HackLab-Oriente/desktop-buddy/docs/services.md

# Servicios de terceros: qué necesitamos y recomendaciones

Precios verificados el 2026-07-13. El contrato de Brain mantiene todo esto
intercambiable — son valores por defecto, no compromisos. Todas las claves
viven en la NVS del dispositivo, se meten por la web UI y nunca van en packs.

## Servicios que necesita el buddy

| Servicio | Para qué | Cuándo | ¿Cuenta? |
|---|---|---|---|
| **LLM** (el Brain) | Personalidad, conversación, elección de emoción | v1 (M2) | Sí |
| **STT** (voz a texto) | Entrada de voz push-to-talk | v1 (M3) | Sí |
| **TTS** (texto a voz) | Respuestas habladas | v1 (M3) | Sí |
| Hora NTP | Reloj, timers, comportamientos de reposo | v1 | No (pool.ntp.org, gratis) |
| Calendario/feeds por polling | Senses opcionales (ICS, RSS) | v2 | No (URLs públicas o con token) |
| Relay de webhooks / túnel | Eventos entrantes sin IP pública | v2 (era del hub) | Capas gratuitas (Cloudflare Tunnel, Tailscale) |

## LLM — el Brain

| Proveedor / modelo | Precio (in/out por MTok) | Por qué sí / por qué no |
|---|---|---|
| **Anthropic Claude Haiku 4.5** ⭐ | $1 / $5 | Rápido, barato y con carácter — para un compañero, la calidad de la personalidad ES el producto. Streaming. **El prompt caching no aplica todavía** — ver abajo. |
| OpenAI clase gpt-4o-mini | ~$0.60 / $2.40 | Algo más barato; su atractivo real es la comodidad de una sola cuenta (ver stacks abajo). |
| Anthropic Claude Sonnet 5 | $3 / $15 ($2/$10 intro) | Sobredimensionado para charla ligera; interesante después para Skills/herramientas en el hub. |

Una interacción típica, **medida sobre el cuerpo que envía el firmware hoy**:
~200 tokens de entrada y ~45 de salida → **~$0.0004 con Haiku**. La estimación
anterior (1.200 in / 150 out, ~$0.002) era unas 4,6 veces pesimista.

**El prompt caching no recorta nada con este prompt.** El prefijo mínimo
cacheable de Claude Haiku 4.5 son **4.096 tokens** y el system prompt de
personalidad son ~160: veinticinco veces corto, así que un `cache_control`
se ignoraría en silencio. Y aunque aplicara, a 50 interacciones diarias
ahorraría ~$0,22 al mes — y como el TTL por defecto son 5 minutos, un buddy
al que se acaricia cada pocas horas fallaría la caché casi siempre y pagaría
el recargo de escritura de 1,25×, saliendo **más caro**.

Mantener el prompt estable byte a byte sigue siendo buena práctica; el ahorro
llega el día que un pack empuje el system prompt más allá de 4.096 tokens
(~16 KB de texto), no antes.

## STT — de voz a texto

La clave: **push-to-talk elimina la necesidad de STT en streaming en v1.**
Soltar el botón = fin de la frase, así que el dispositivo puede hacer un POST
HTTPS con el clip completo (unos segundos de WAV) y recibir el texto. Eso es
radicalmente más simple en el ESP32 que un WebSocket de streaming — un POST
multipart con `esp_http_client` y ya.

| Proveedor | Precio | Modo | Encaje en ESP32 |
|---|---|---|---|
| **OpenAI gpt-4o-mini-transcribe** ⭐ | ~$0.003/min ($0.18/hora) | POST por lotes (existe variante realtime) | **Mismo host que el TTS**: una clave, un certificado, una conexión TLS reutilizable. Ver abajo. |
| Groq Whisper large-v3-turbo | $0.04/hora, **facturación mínima de 10 s por petición** | POST por lotes, ~217× tiempo real (un clip de 5 s se transcribe en decenas de ms) | Inferencia mucho más rápida y capa gratuita real (2.000 peticiones/día). Un host TLS más, y 20 req/min **por organización**. |
| Deepgram Nova-3 | $0.0048/min streaming | Streaming por WebSocket | Ver fila de abajo. |

### Por qué el STT cambió de Groq a OpenAI

La primera versión de este documento elegía Groq por precio. El análisis no
estaba mal; el precio resultó ser el eje **menos** importante a nuestra escala.

**El precio no decide.** El titular de Groq es $0,04/h contra $0,18/h — 4,5×
más barato. Pero Groq **factura un mínimo de 10 s por petición**, y un buddy
push-to-talk manda clips de 2–5 s. Por debajo de **2,2 s OpenAI sale más
barato**, y en la duración típica la diferencia se queda en 1,4×. Un taller
entero —15 personas, 4 sesiones, ~30 interacciones cada una— son **1.800
transcripciones: $0,20 con Groq contra $0,27 con OpenAI. Siete centavos.**

**Lo que sí decide: un host TLS menos.** Cada turno de voz habla con STT →
Claude → TTS. Con Groq son **tres hosts distintos**; con OpenAI haciendo STT y
TTS son **dos**, y esa conexión se puede mantener viva a través de la llamada
al cerebro. Importa porque una conexión TLS cuesta **~50 KB de RAM interna**
(ver [architecture.md](architecture.md)), justo la memoria escasa —los búferes
DMA y el WiFi no pueden vivir en PSRAM—, y porque un handshake mbedTLS en el
ESP32 se mide en cientos de milisegundos contra un presupuesto total de
1,5–3 s. Groq gana en inferencia (decenas de ms contra unos cientos), pero ese
ahorro es más pequeño que un handshake entero.

> **Esto último está sin medir.** Es la única cifra que podría darle la vuelta
> a la decisión: si el handshake resulta barato con reanudación de sesión,
> Groq gana por velocidad. Medirlo es tarea del track de voz.

**La trampa de la capa gratuita.** Groq regala 2.000 peticiones/día sin
tarjeta, que para un hacklab vale. Pero el límite son **20 peticiones/minuto
por organización**, y varias claves no lo multiplican: 15 personas pulsando
cada 30 s son 30 req/min, **por encima del límite**. Solo funciona si cada uno
se hace su propia cuenta, que es un paso más de instalación por quince.

**Qué haría cambiar la decisión:** transcripción larga (grabar una reunión, no
una frase), donde el 4,5× de Groq sí es dinero; o un handshake medido barato.

## ¿Y hacer todo el flujo con un solo proveedor?

**Con Anthropic no se puede: no tiene STT ni TTS.** Su API es texto e imagen de
entrada, texto de salida. Claude puede ser el cerebro; nunca los oídos ni la
boca.

**Y el cerebro no se mueve a OpenAI solo por fontanería.** El argumento del host
TLS que ganó para el STT pierde aquí: transcribir y hablar son commodities
—cambiar de proveedor cambia una cifra en la factura— mientras que **el cerebro
es la única pieza cuya elección se *oye* como personalidad**, que es lo que este
proyecto dice estar vendiendo. La diferencia de coste son ~$1,80 en todo el
taller, y mantener la opción abierta ya está pagado: el contrato de cerebro es
un adaptador con backends intercambiables.

## TTS — de texto a voz

Restricción: el ESP32 quiere **PCM o MP3 en streaming de vuelta** (decodificar
MP3 con libhelix/minimp3 es barato; PCM crudo a 16k/22k es aún más fácil).
Los tres de abajo pueden dar ambos.

| Proveedor | Precio | Por qué sí / por qué no |
|---|---|---|
| **OpenAI gpt-4o-mini-tts** ⭐ | ~$0.015/min de audio ($0.60/MTok texto de entrada, $12/MTok audio de salida) | Barato, buena calidad, ~13 voces, admite "instrucciones" de voz (tono/carácter — útil para packs de personalidad). |
| Groq PlayAI Dialog / Orpheus | $50 / $22 por millón de caracteres | Orpheus sale barato, pero devuelve el tercer host TLS y sus variantes publicadas son inglés y árabe — **para un buddy que habla español hay que verificarlo antes de considerarlo**. |
| ElevenLabs Flash v2.5 | $0.05/1k caracteres, **con mínimo de facturación de 1.000 caracteres** | Las mejores voces con carácter + clonado, y 75 ms de latencia. Pero una respuesta de 150 caracteres factura como 1.000: **$0,05 por respuesta, 20× OpenAI** (ver abajo). |
| Deepgram Aura-2 | ~$0.03–0.05/1k caracteres | Baja latencia, API simple; atractivo de bundle si ya estás en Deepgram para STT. |

### El TTS es donde está el dinero — y el mínimo de ElevenLabs

Una respuesta hablada del buddy son ~150 caracteres (~10 s de audio). Con eso:

| TTS | por respuesta | taller (1.800) | ×OpenAI |
|---|---|---|---|
| **OpenAI gpt-4o-mini-tts** ⭐ | $0,0025 | **$4,50** | 1× |
| Groq Orpheus (inglés) | $0,0033 | $5,94 | 1× |
| Groq PlayAI Dialog | $0,0075 | $13,50 | 3× |
| ElevenLabs Flash v2.5 | $0,0500 | **$90,00** | **20×** |

Dos cosas que corregir de la versión anterior de este documento:

1. **ElevenLabs decía «≈$0,0075 por respuesta»: era 6,7× optimista.** Dividía la
   tarifa y no veía el **mínimo de 1.000 caracteres por petición**. Nuestras
   respuestas son de 150.
2. **El TTS cuesta ~17× lo que el STT.** Toda la discusión de Groq contra
   OpenAI para transcribir se peleaba por siete centavos mientras el gasto real
   estaba en la fila de abajo.

> **Regla, no anécdota: mira siempre el mínimo de facturación antes que la
> tarifa.** Nos ha pasado dos veces —los 10 s de Groq en STT, los 1.000
> caracteres de ElevenLabs en TTS— y las dos veces el titular mentía. Un buddy
> habla a ráfagas de una frase; a esa escala **el mínimo manda sobre la
> tarifa**. Cualquier proveedor nuevo se evalúa con el coste de *una respuesta
> nuestra*, no con el precio por hora o por millón.

**ElevenLabs no está descartado: está aplazado.** $90 por taller es asequible
si el grupo decide que una voz propia *es* el producto — eso es una decisión de
personalidad, no un problema de presupuesto. La razón para esperar es otra:
**todavía nadie sabe cómo debe sonar el buddy.** Mientras tanto, el parámetro
`instructions` de OpenAI deja que cada pack ajuste el tono. Se revisa cuando
[#24](https://github.com/HackLab-Oriente/desktop-buddy/issues/24) y las
decisiones de personalidad hayan producido un carácter concreto.

## Coste por interacción (el número que importa)

Un intercambio PTT ≈ 8 s de voz del usuario + respuesta hablada de ~150
caracteres:

| Pieza | Stack recomendado | Coste |
|---|---|---|
| STT (OpenAI mini-transcribe) | 8 s a $0.003/min | ~$0.0004 |
| LLM (Haiku 4.5) | ~200 in / 45 out | ~$0.0004 |
| TTS (OpenAI mini-tts) | ~10 s de audio | ~$0.0025 |

El TTS es la partida más grande de las tres — y con ElevenLabs sería **$0,05**,
veinte veces el total actual.
| **Total** | | **≈ medio centavo** |

Con un uso intenso de 50 interacciones/día: **~$7/mes por buddy**. Las
interacciones solo-chirp (reflejos, gestos) no cuestan nada; el chat de texto
por web solo paga la parte del LLM.

## Stacks recomendados

- **Recomendado:** Claude Haiku 4.5 (cerebro) + OpenAI para **voz entera**
  (mini-transcribe + mini-tts). **Dos cuentas y dos hosts TLS**, no tres. La
  diferencia de coste contra meter Groq es de centavos; la de fontanería, no.
- **Menos cuentas (para amigos):** solo OpenAI — gpt-4o-mini (cerebro) +
  gpt-4o-mini-transcribe + gpt-4o-mini-tts. Una sola clave que pegar en la
  web UI. La web debería soportar ambos presets; el contrato de Brain hace
  que el proveedor sea un desplegable, no un fork.
- **Mejora de voz con carácter:** cambia el TTS a ElevenLabs Flash v2.5
  cuando un pack quiera una voz distintiva.

## Notas de implementación

- **El streaming de la respuesta del LLM importa más que el del STT.**
  Streamea la respuesta de Haiku para que la cara/emoción reaccione según
  llega el texto, y el TTS pueda empezar con la primera frase — ahí se gana
  la latencia percibida.
- **Prompt caching:** mantén el system prompt de personalidad estable byte a
  byte para que la caché de Anthropic recorte ~90% del coste de entrada en
  interacciones repetidas.
- Todos los proveedores de aquí son TLS + token bearer sobre HTTPS/WebSocket
  — todo amigable para el ESP32; no hace falta baile OAuth en v1 (las
  integraciones OAuth-osas son exactamente para lo que existe el hub de v2).

### Fuentes

- [Precios de Deepgram](https://deepgram.com/pricing) · [Desglose de tarifas Nova-3](https://brasstranscripts.com/blog/deepgram-pricing-per-minute-2025-real-time-vs-batch)
- [Groq Whisper large-v3-turbo](https://groq.com/blog/whisper-large-v3-turbo-now-available-on-groq-combining-speed-quality-for-speech-recognition) · [Guía de precios de Groq](https://www.eesel.ai/blog/groq-pricing)
- [Precios de transcripción de OpenAI](https://costgoat.com/pricing/openai-transcription) · [Precios de gpt-4o-mini-tts](https://tokenmix.ai/blog/gpt-4o-mini-tts-cheapest-tts-api-2026)
- [Precios de la API de ElevenLabs](https://elevenlabs.io/pricing/api)
- Precios de modelos Anthropic: docs de la Claude API (Haiku 4.5 $1/$5, Sonnet 5 $3/$15 por MTok)
